circircir-circle/human_exist_device/assets/image-20220725195918034-16587506420202.png

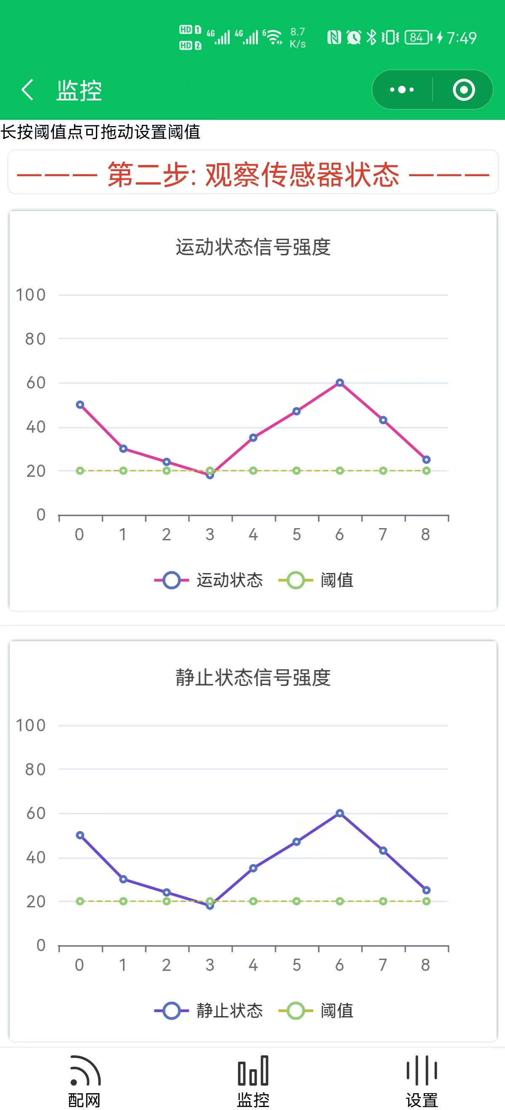
assets/image-20220725195918034-16587506420202.png
