circircir-circle/human_exist_device/assets/image-20220725200420268.png

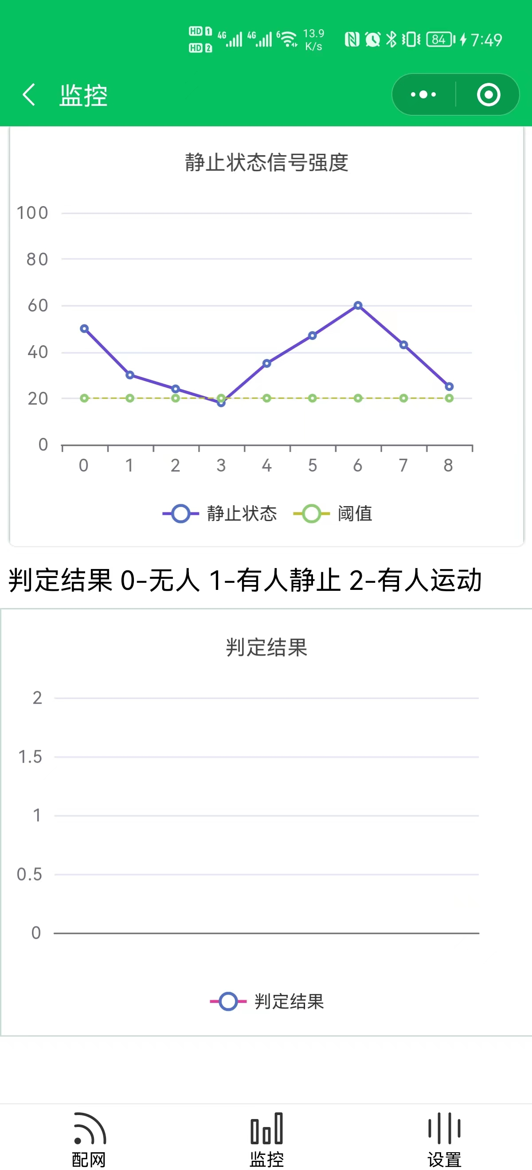
assets/image-20220725200420268.png
